thehonker/weathernerd/local-storage/firmware/esp32c6-supermini/main/oled_font.h

/*
 * WeatherNerd — 8×8 ASCII font for SH1106 OLED
 *
 * Printable ASCII 0x20-0x7F (96 characters, 8 bytes each = 768 bytes).
 * Each byte is one row, MSB = leftmost pixel, 8 rows per character.
 * Standard font8x8_basic — public domain.
 */

#pragma once

#include <stdint.h>

static const uint8_t oled_font[] = {
    /* 0x20 ' ' */ 0x00,0x00,0x00,0x00,0x00,0x00,0x00,0x00,
    /* 0x21 '!' */ 0x18,0x3C,0x3C,0x18,0x18,0x00,0x18,0x00,
    /* 0x22 '"' */ 0x36,0x36,0x00,0x00,0x00,0x00,0x00,0x00,
    /* 0x23 '#' */ 0x36,0x36,0x7F,0x36,0x7F,0x36,0x36,0x00,
    /* 0x24 '$' */ 0x0C,0x3E,0x03,0x1E,0x30,0x1F,0x0C,0x00,
    /* 0x25 '%' */ 0x00,0x63,0x33,0x18,0x0C,0x66,0x63,0x00,
    /* 0x26 '&' */ 0x1C,0x36,0x1C,0x6E,0x3B,0x33,0x6E,0x00,
    /* 0x27 ''' */ 0x06,0x06,0x03,0x00,0x00,0x00,0x00,0x00,
    /* 0x28 '(' */ 0x18,0x0C,0x06,0x06,0x06,0x0C,0x18,0x00,
    /* 0x29 ')' */ 0x06,0x0C,0x18,0x18,0x18,0x0C,0x06,0x00,
    /* 0x2A '*' */ 0x00,0x66,0x3C,0xFF,0x3C,0x66,0x00,0x00,
    /* 0x2B '+' */ 0x00,0x0C,0x0C,0x3F,0x0C,0x0C,0x00,0x00,
    /* 0x2C ',' */ 0x00,0x00,0x00,0x00,0x00,0x0C,0x0C,0x06,
    /* 0x2D '-' */ 0x00,0x00,0x00,0x3F,0x00,0x00,0x00,0x00,
    /* 0x2E '.' */ 0x00,0x00,0x00,0x00,0x00,0x0C,0x0C,0x00,
    /* 0x2F '/' */ 0x00,0x60,0x30,0x18,0x0C,0x06,0x03,0x00,
    /* 0x30 '0' */ 0x3E,0x63,0x73,0x7B,0x6F,0x67,0x3E,0x00,
    /* 0x31 '1' */ 0x0C,0x0E,0x0C,0x0C,0x0C,0x0C,0x3F,0x00,
    /* 0x32 '2' */ 0x1E,0x33,0x30,0x1C,0x06,0x33,0x3F,0x00,
    /* 0x33 '3' */ 0x1E,0x33,0x1C,0x1C,0x30,0x33,0x1E,0x00,
    /* 0x34 '4' */ 0x38,0x3C,0x36,0x33,0x7F,0x30,0x78,0x00,
    /* 0x35 '5' */ 0x3F,0x03,0x1F,0x30,0x30,0x33,0x1E,0x00,
    /* 0x36 '6' */ 0x1C,0x06,0x03,0x1F,0x33,0x33,0x1E,0x00,
    /* 0x37 '7' */ 0x3F,0x33,0x30,0x18,0x0C,0x0C,0x0C,0x00,
    /* 0x38 '8' */ 0x1E,0x33,0x33,0x1E,0x33,0x33,0x1E,0x00,
    /* 0x39 '9' */ 0x1E,0x33,0x33,0x3E,0x30,0x18,0x0C,0x00,
    /* 0x3A ':' */ 0x00,0x0C,0x0C,0x00,0x00,0x0C,0x0C,0x00,
    /* 0x3B ';' */ 0x00,0x0C,0x0C,0x00,0x00,0x0C,0x0C,0x06,
    /* 0x3C '<' */ 0x18,0x0C,0x06,0x03,0x06,0x0C,0x18,0x00,
    /* 0x3D '=' */ 0x00,0x00,0x3F,0x00,0x3F,0x00,0x00,0x00,
    /* 0x3E '>' */ 0x06,0x0C,0x18,0x30,0x18,0x0C,0x06,0x00,
    /* 0x3F '?' */ 0x1E,0x33,0x30,0x18,0x0C,0x00,0x0C,0x00,
    /* 0x40 '@' */ 0x3E,0x63,0x7B,0x7B,0x7B,0x03,0x1E,0x00,
    /* 0x41 'A' */ 0x0C,0x1E,0x33,0x33,0x3F,0x33,0x33,0x00,
    /* 0x42 'B' */ 0x3F,0x66,0x66,0x3E,0x66,0x66,0x3F,0x00,
    /* 0x43 'C' */ 0x3C,0x66,0x03,0x03,0x03,0x66,0x3C,0x00,
    /* 0x44 'D' */ 0x1F,0x36,0x66,0x66,0x66,0x36,0x1F,0x00,
    /* 0x45 'E' */ 0x7F,0x46,0x16,0x1E,0x16,0x46,0x7F,0x00,
    /* 0x46 'F' */ 0x7F,0x46,0x16,0x1E,0x16,0x06,0x0F,0x00,
    /* 0x47 'G' */ 0x3C,0x66,0x03,0x03,0x73,0x66,0x7C,0x00,
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
};
